kholia/HF-PA-v5/datasheets/5v-regulator-circuit.gif

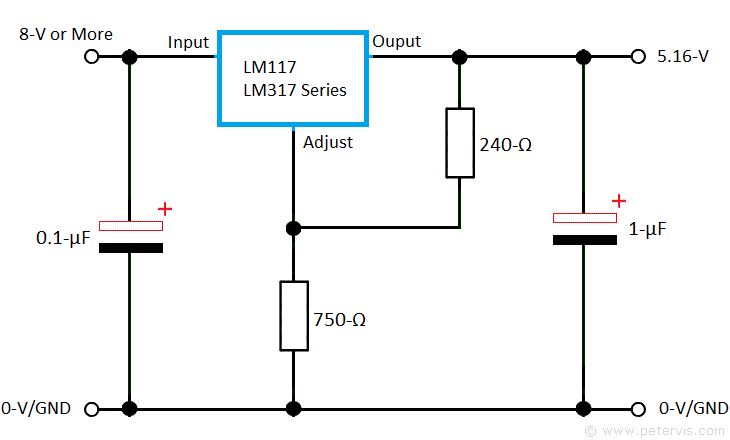
datasheets/5v-regulator-circuit.gif
