kholia/HF-PA-v5/datasheets/irf510-pinout-equivalent.gif

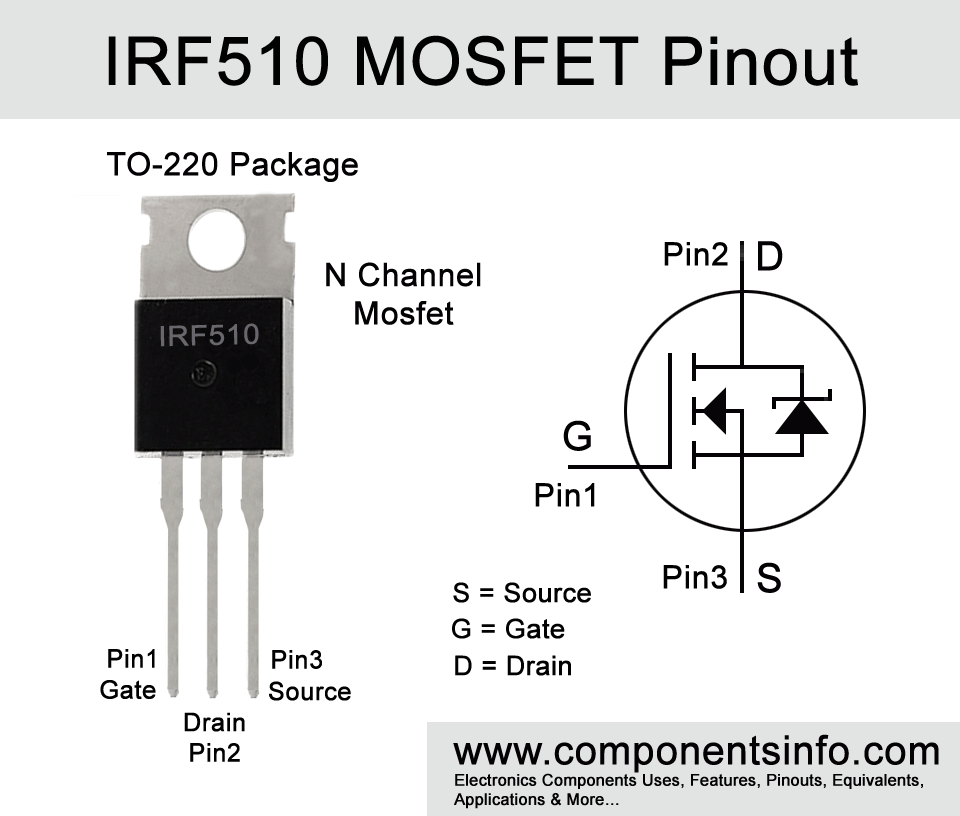
datasheets/irf510-pinout-equivalent.gif
