kholia/HF-PA-v5/datasheets/LM317-voltage-source.png

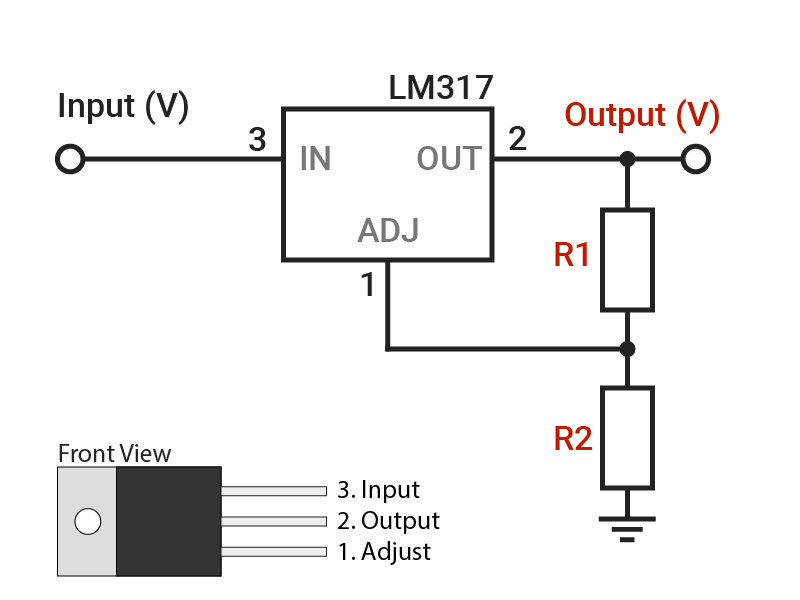
datasheets/LM317-voltage-source.png
