kholia/HF-PA-v5/Info/5W HF PA - Hans.png

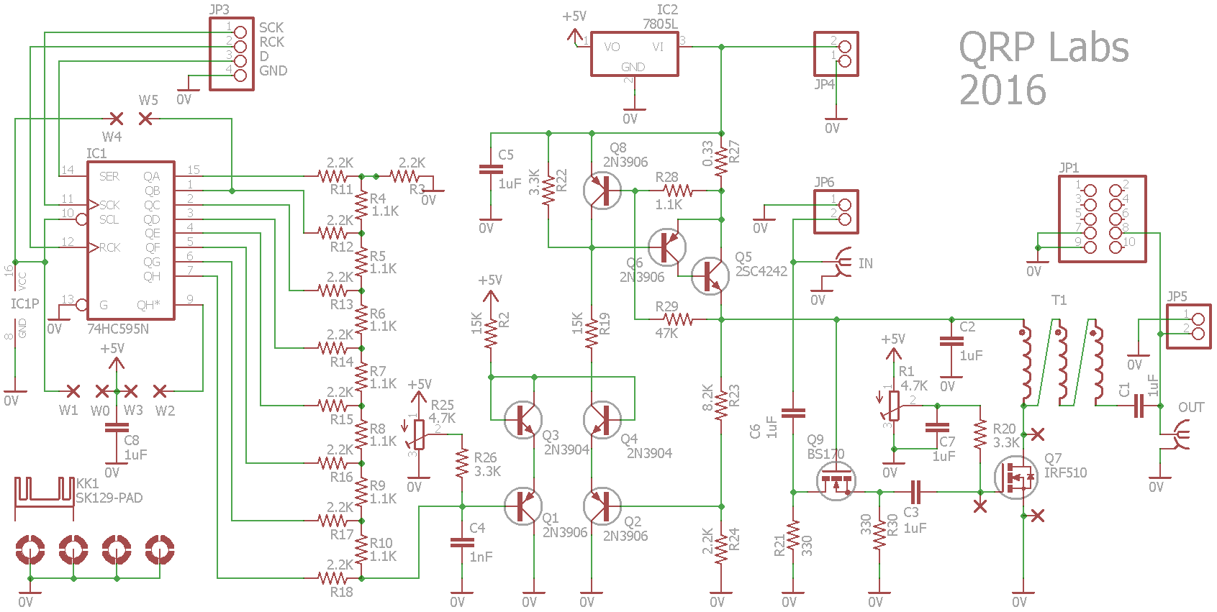
Info/5W HF PA - Hans.png
