kholia/HF-PA-v5/Info/10W HF Linear PA - Hans.png

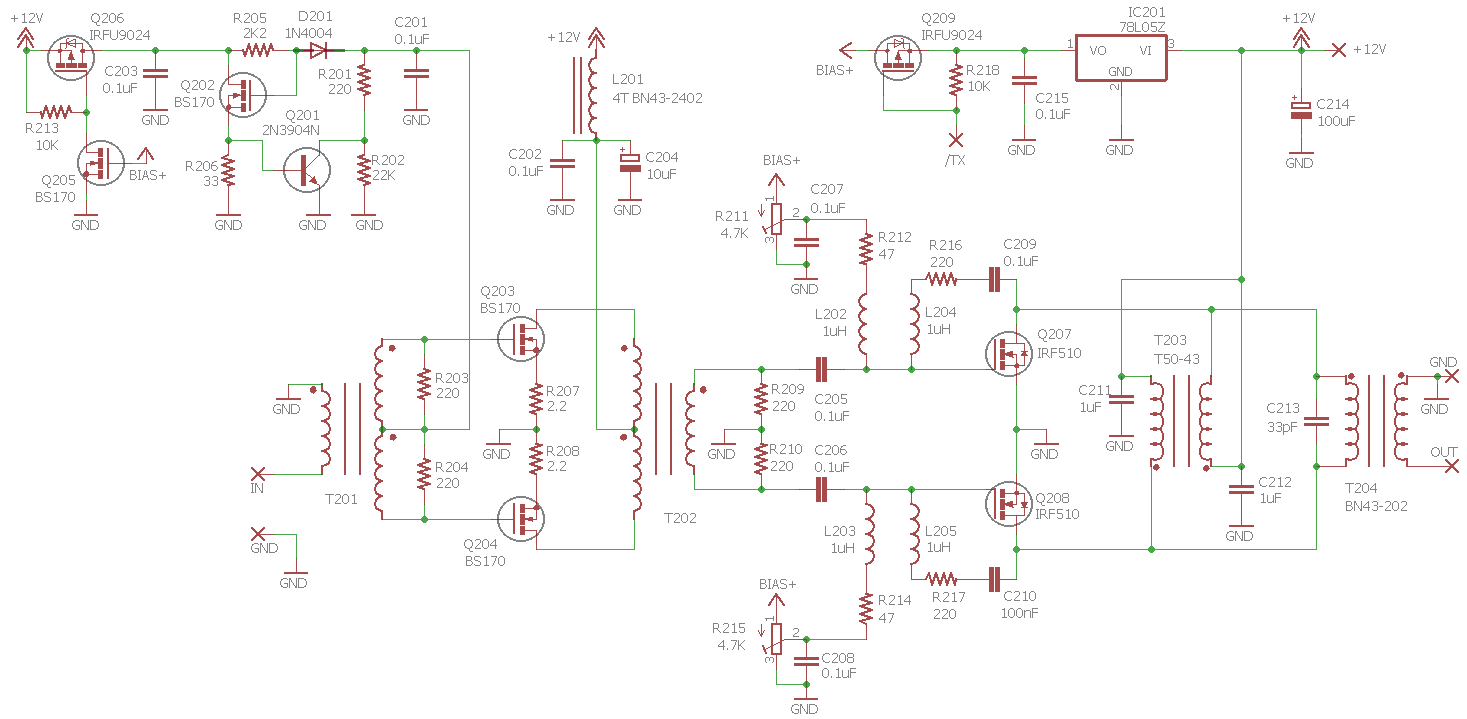
Info/10W HF Linear PA - Hans.png
