kholia/HF-PA-v5/Info/15-02-2021-11-56-602a616ec8522.jpeg

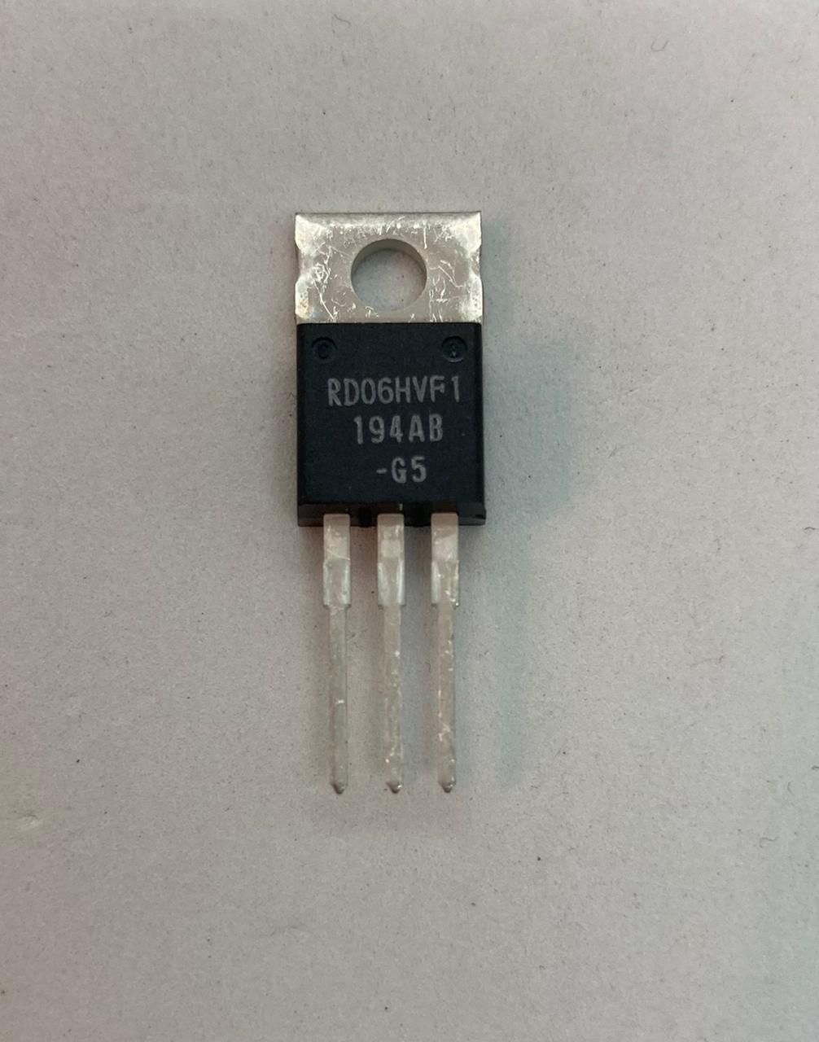
Info/15-02-2021-11-56-602a616ec8522.jpeg
