kholia/HF-PA-v5/Info/15-02-2021-11-57-602a61b2251c0.jpeg

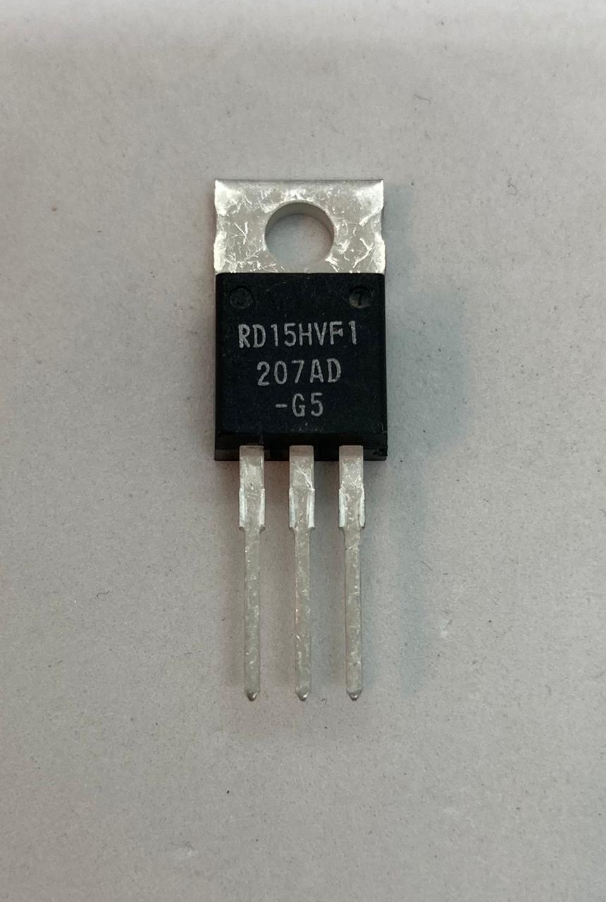
Info/15-02-2021-11-57-602a61b2251c0.jpeg
