kholia/HF-PA-v5/Info/28M5Wamp1.png

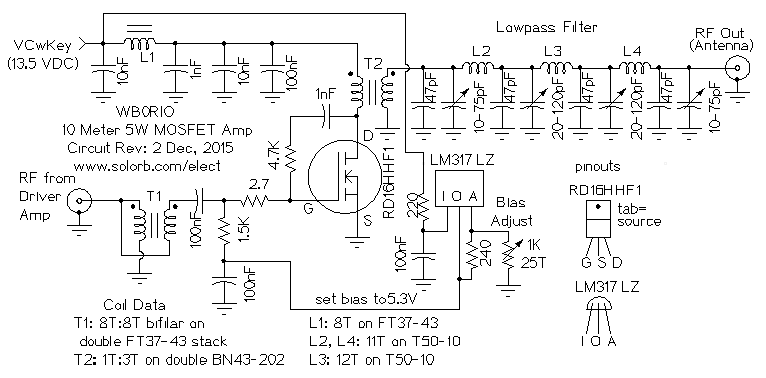
Info/28M5Wamp1.png
