kholia/HF-PA-v5/Info/1367.jpg

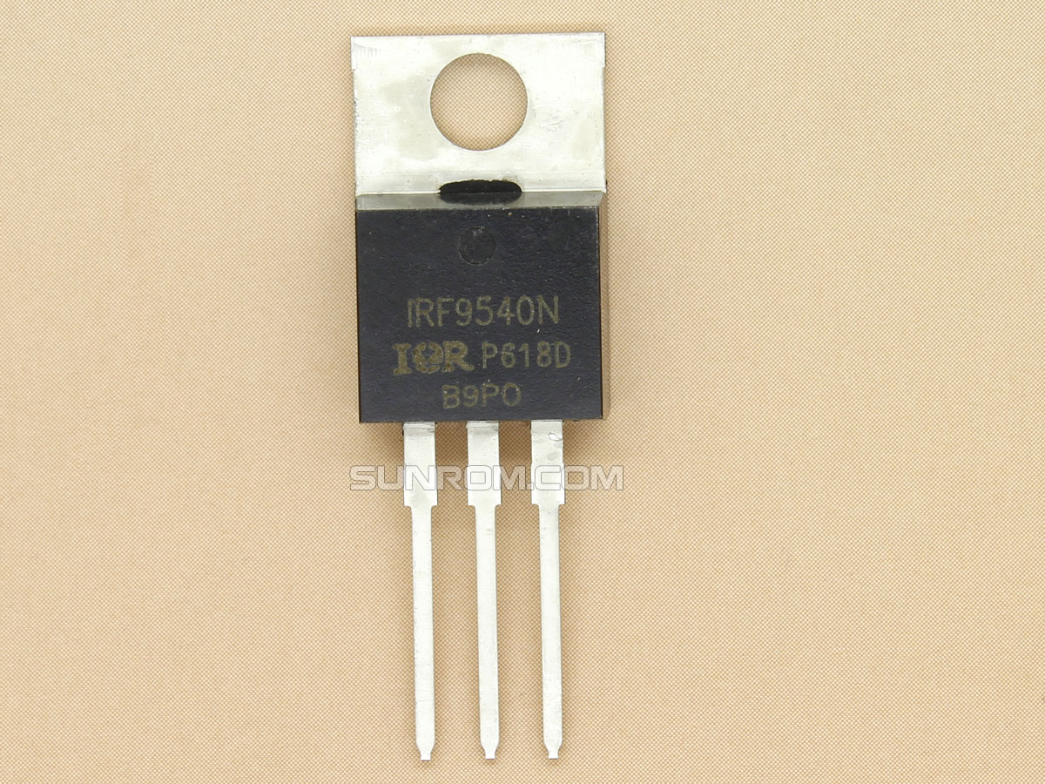
Info/1367.jpg
