kholia/HF-PA-v5/Info/2022-01-05 23.05.50.jpg

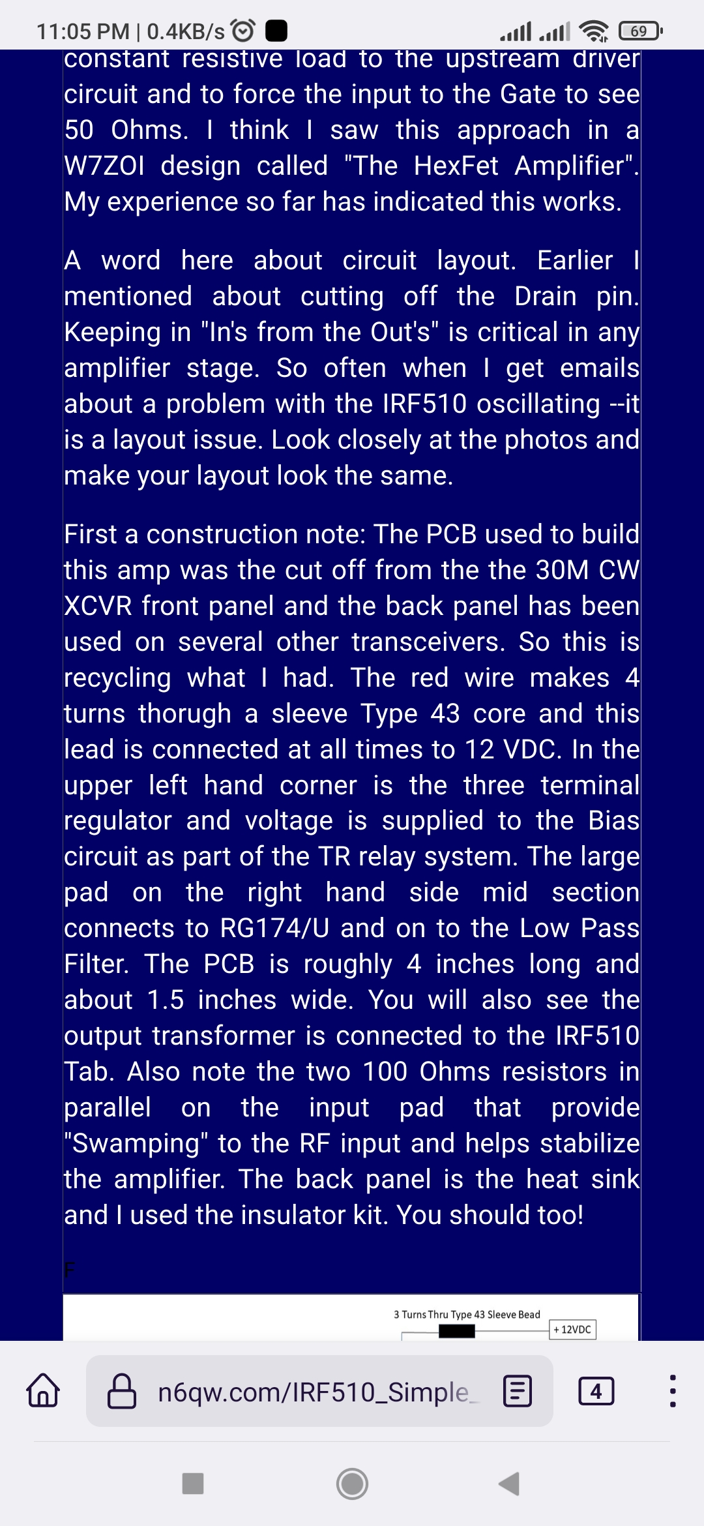
Info/2022-01-05 23.05.50.jpg
