kholia/HF-PA-v5/Info/2022-01-08 22.07.23.jpg

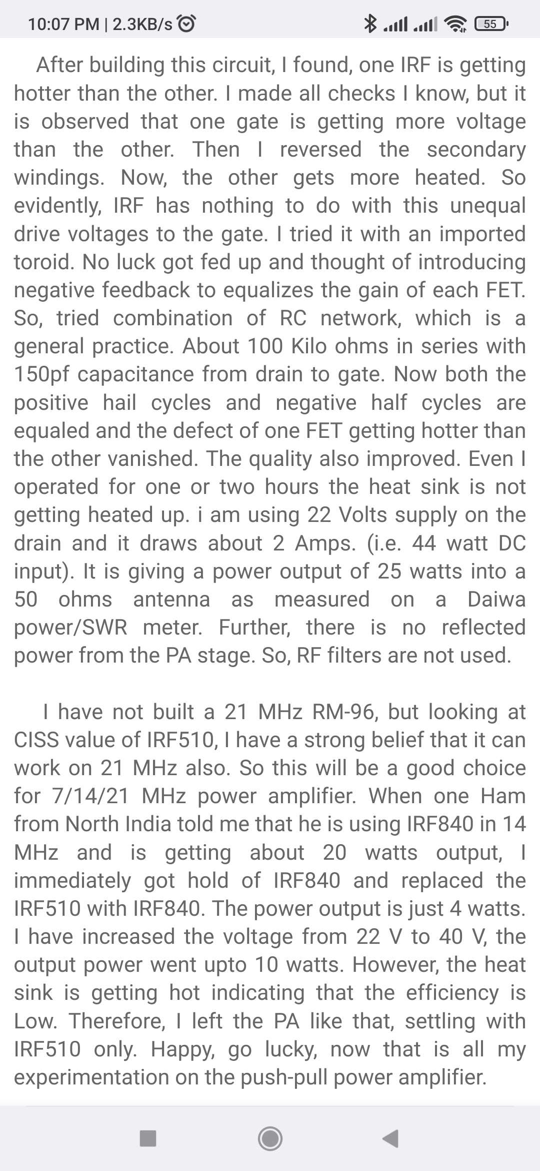
Info/2022-01-08 22.07.23.jpg
