kholia/HF-PA-v5/Info/2022-01-08 22.09.43.jpg

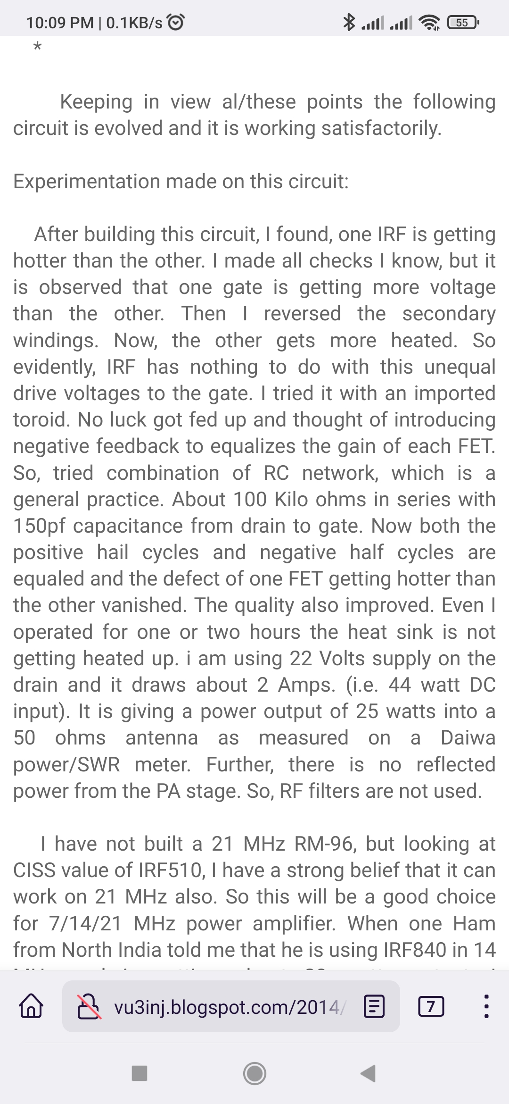
Info/2022-01-08 22.09.43.jpg
