kholia/HF-PA-v5/Info/Aluminium U Type Heat Sink 1.jpg

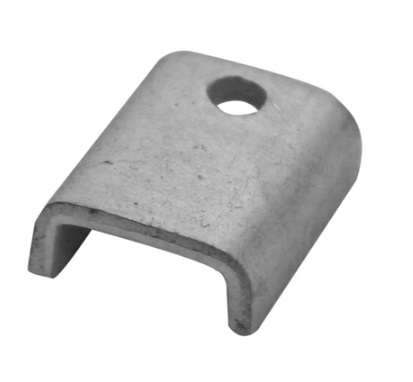
Info/Aluminium U Type Heat Sink 1.jpg
