kholia/HF-PA-v5/Info/Heatsink TO-220.jpg

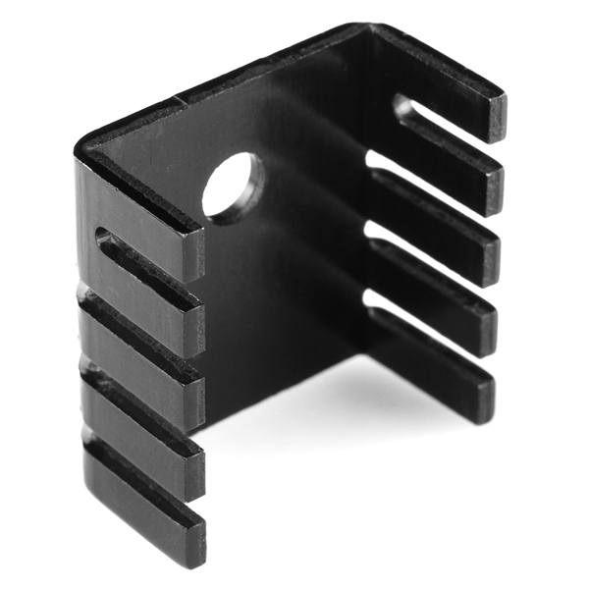
Info/Heatsink TO-220.jpg
