kholia/HF-PA-v5/Info/Hex-Inverter-As-MOSFET-Driver.gif

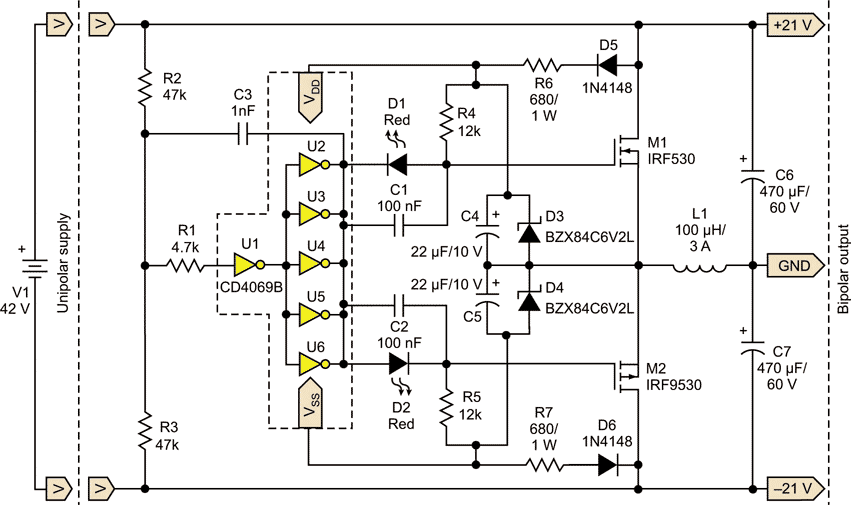
Info/Hex-Inverter-As-MOSFET-Driver.gif
