kholia/HF-PA-v5/Info/Hot mashup idea - was found independently on TG first.png

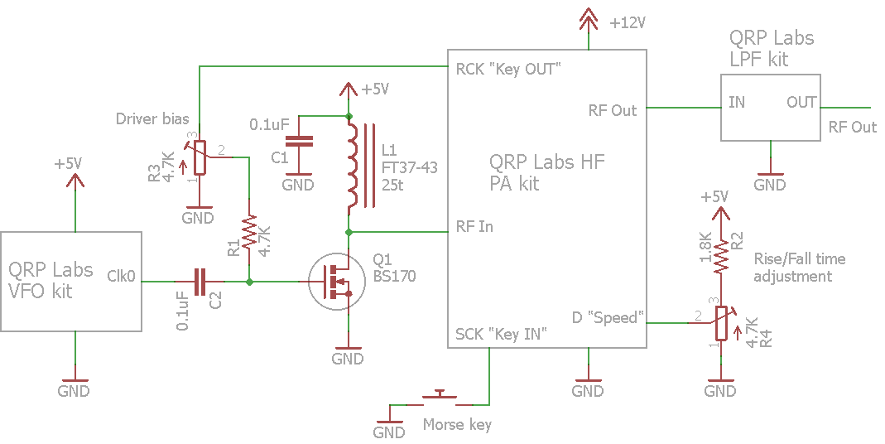
Info/Hot mashup idea - was found independently on TG first.png
