kholia/HF-PA-v5/Info/KB1GMX note.png

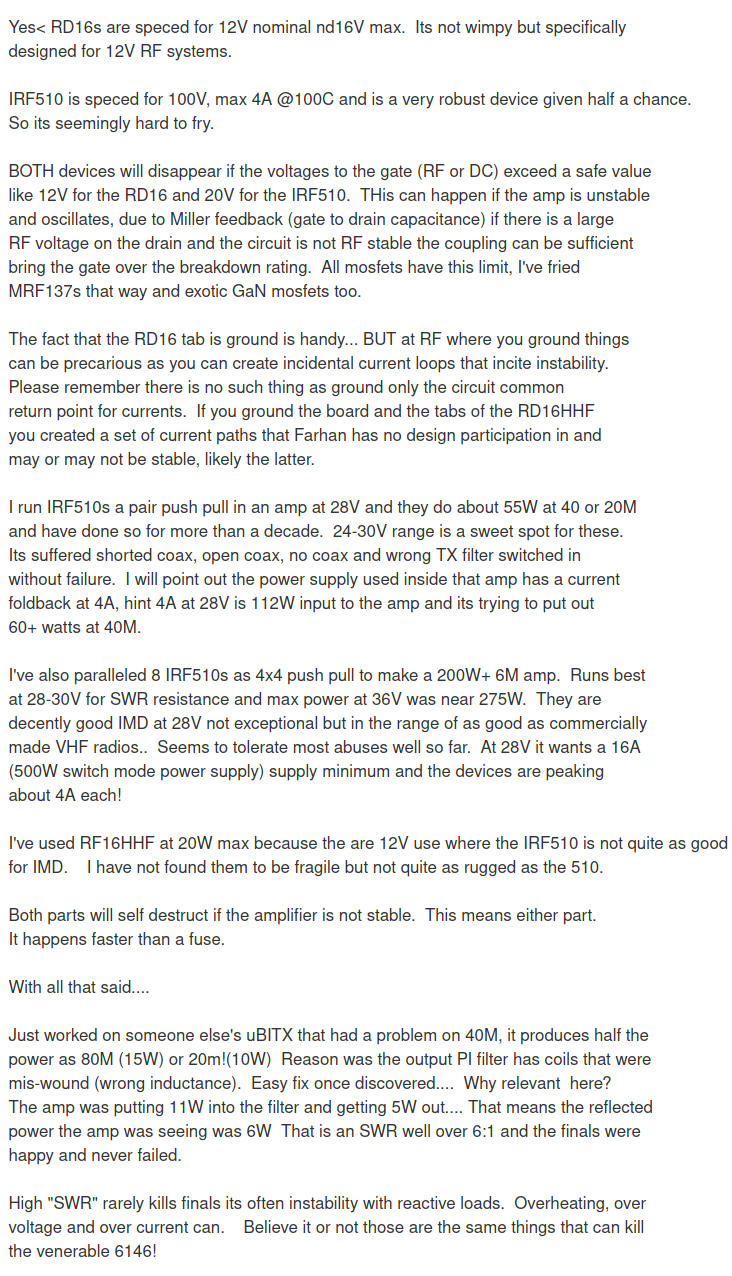
Info/KB1GMX note.png
