kholia/HF-PA-v5/Info/MTR5B PA.png

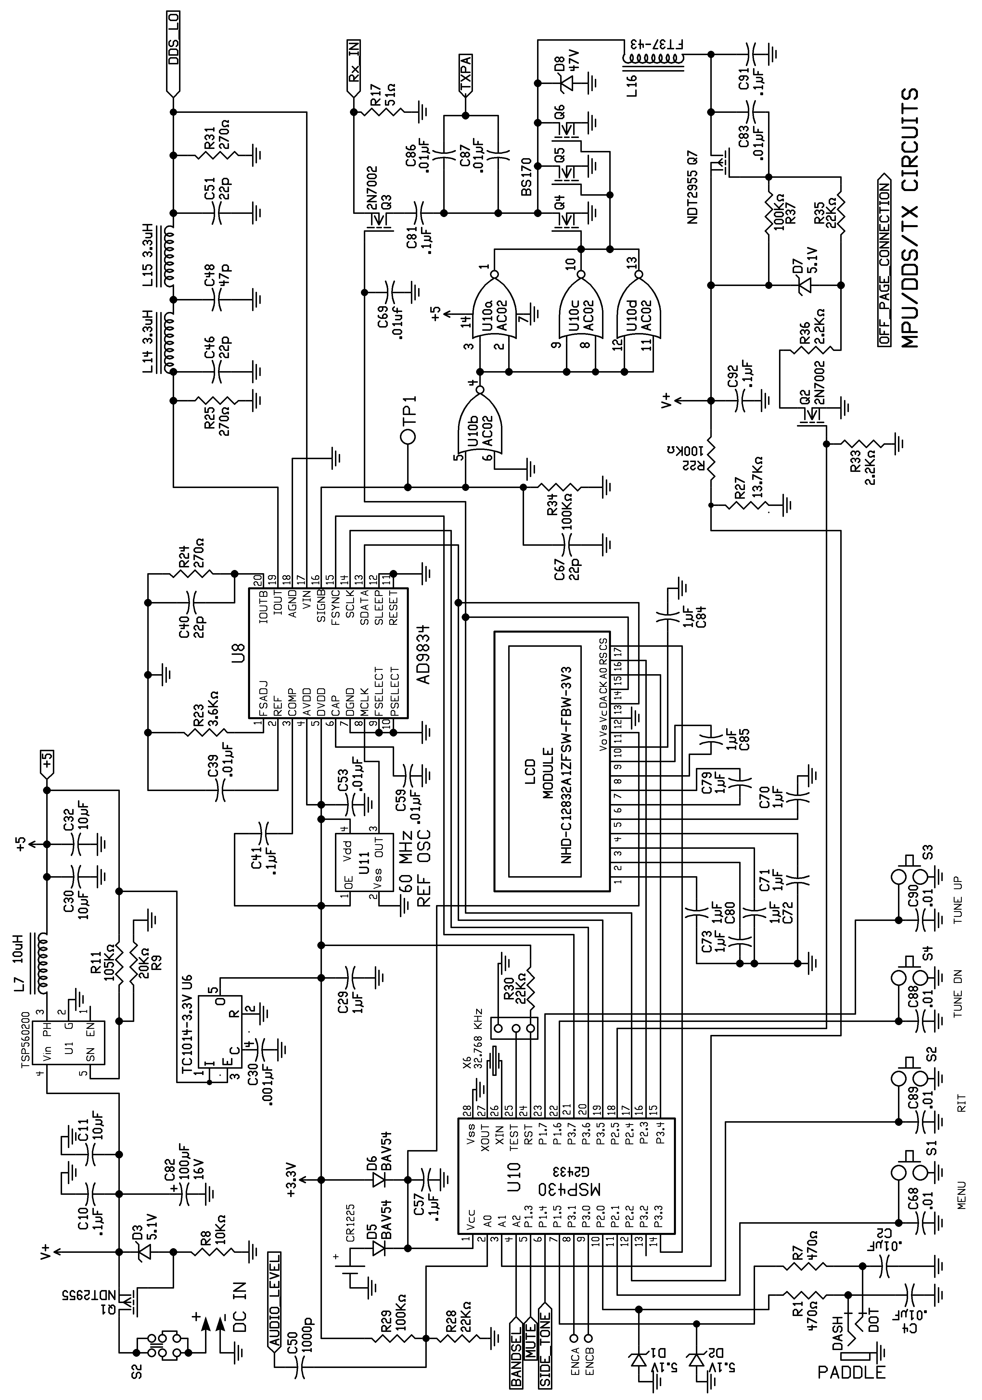
Info/MTR5B PA.png
