kholia/HF-PA-v5/Info/PFR-3-TX.png

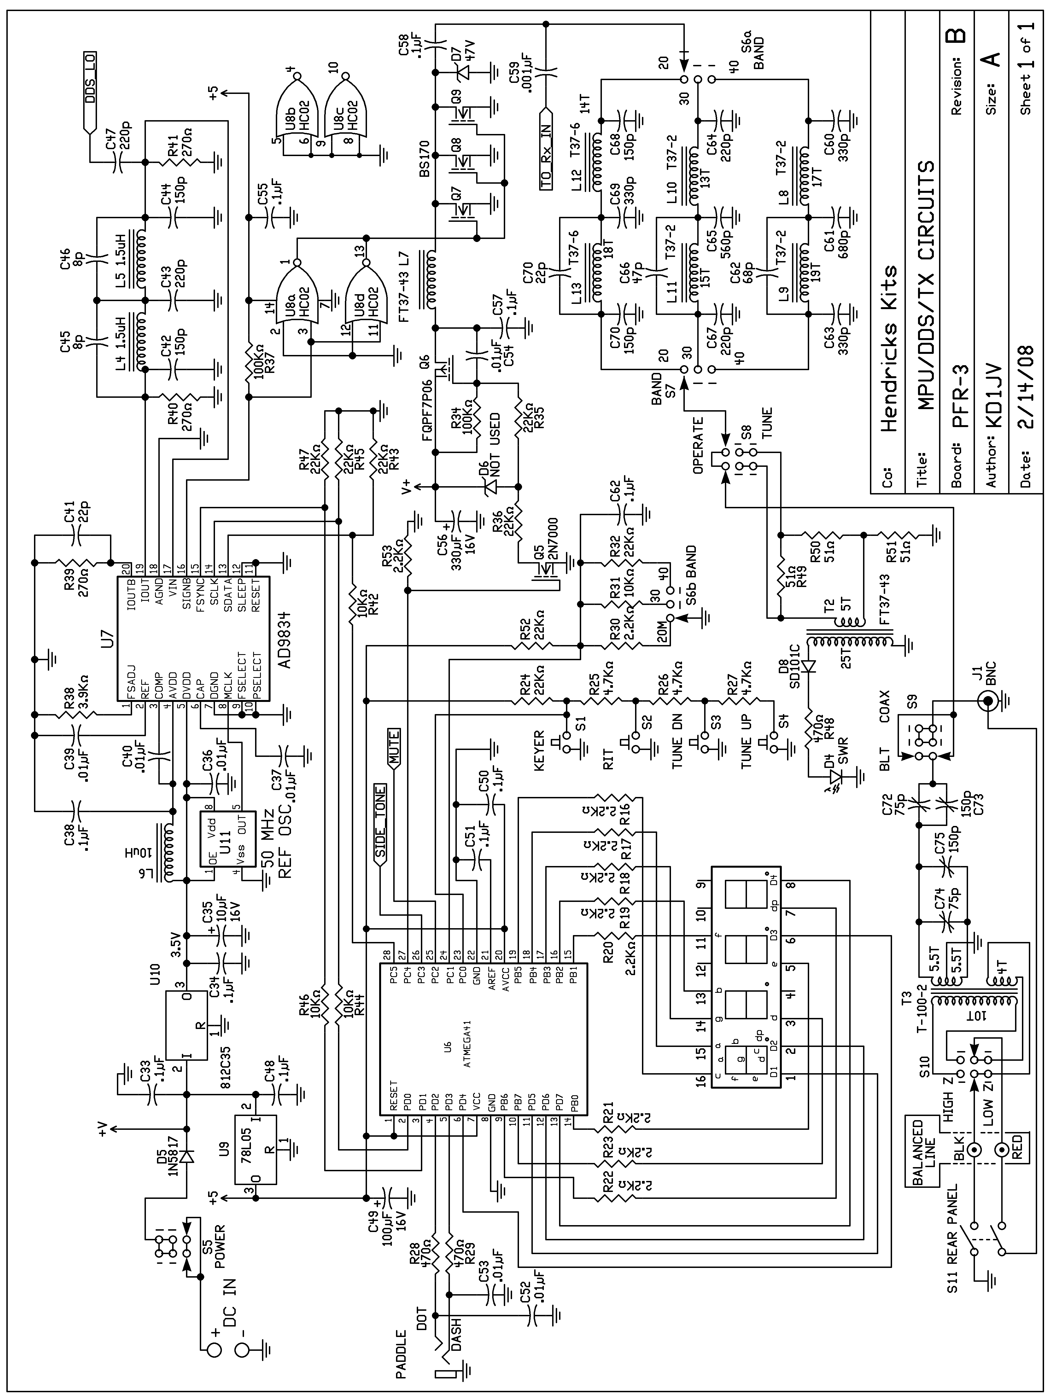
Info/PFR-3-TX.png
