kholia/HF-PA-v5/Info/RM065-672x378.jpg

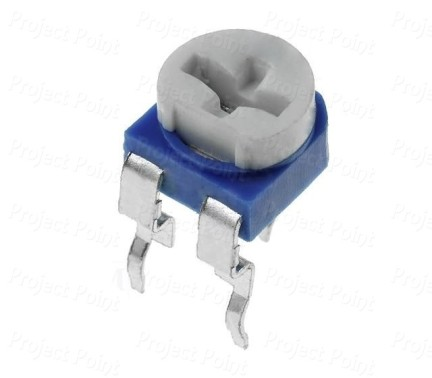
Info/RM065-672x378.jpg
