kholia/HF-PA-v5/Info/Screenshot_2022-01-20_20-48-25.png

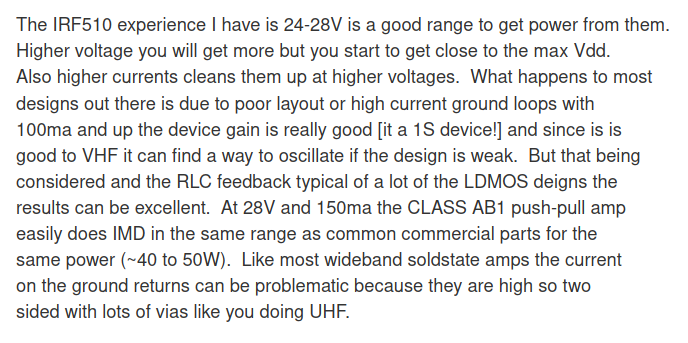
Info/Screenshot_2022-01-20_20-48-25.png
