kholia/HF-PA-v5/Info/Screenshot_2022-03-04_15-51-50.png

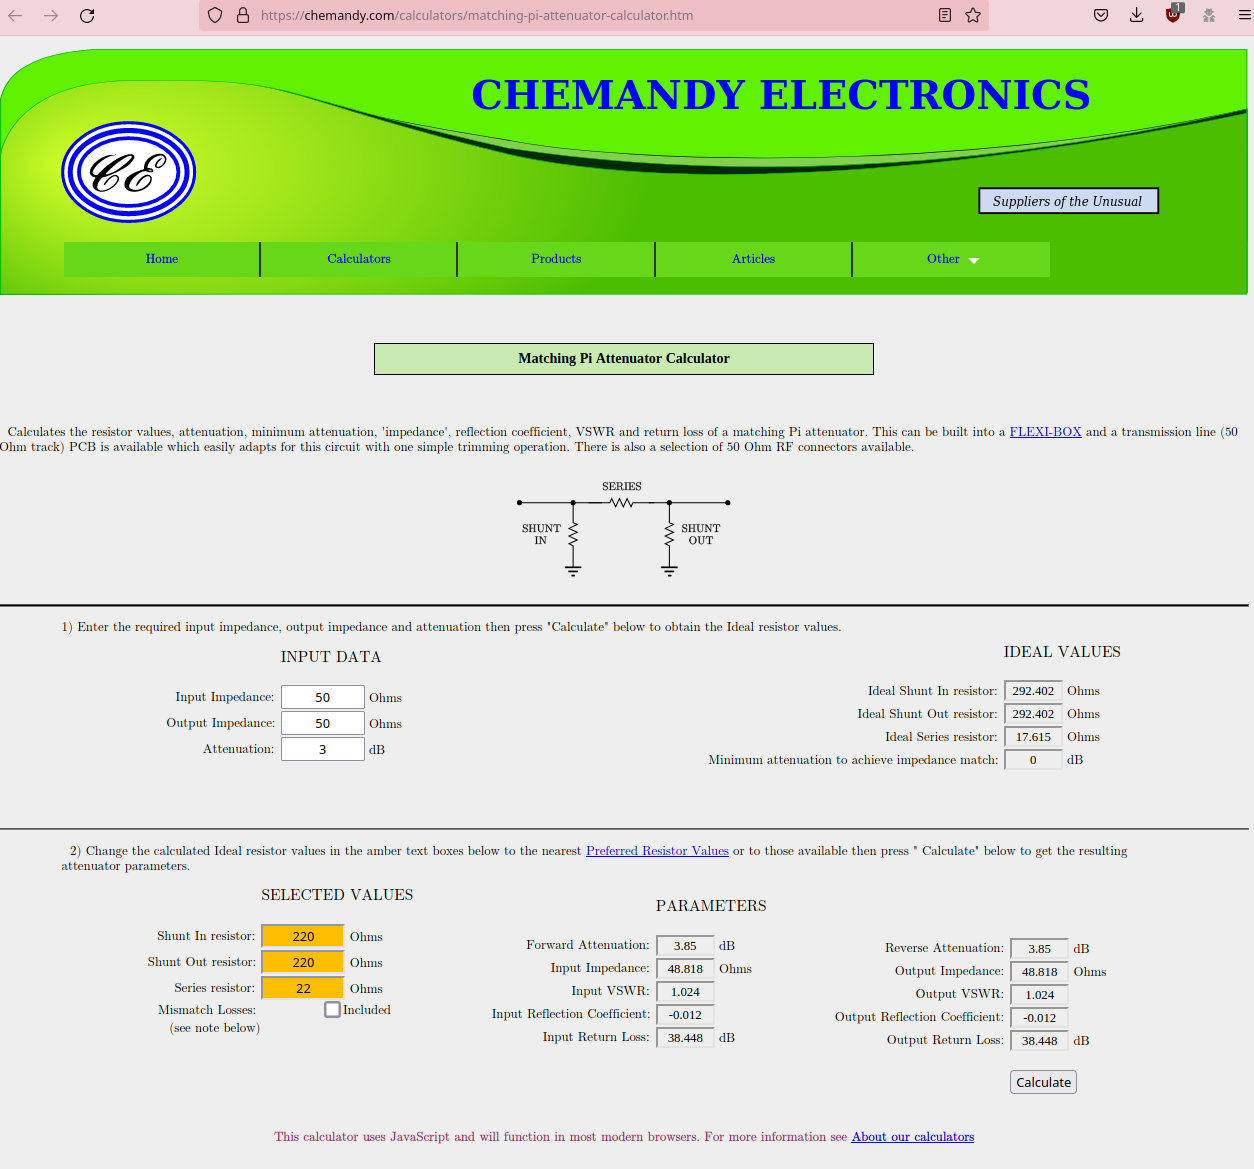
Info/Screenshot_2022-03-04_15-51-50.png
