kholia/HF-PA-v5/Info/Stability-2-ARRL-Chapter-17-2019.png

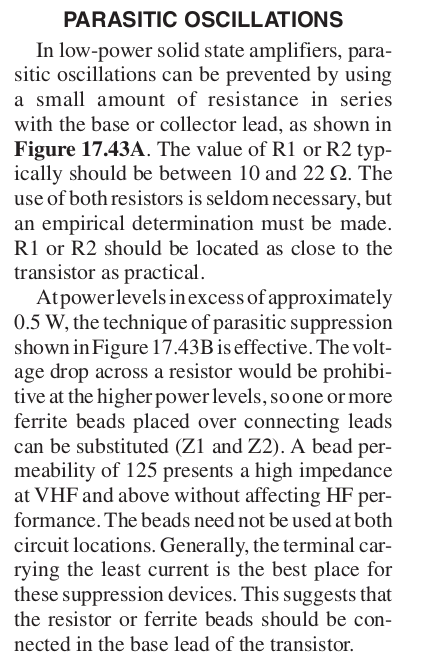
Info/Stability-2-ARRL-Chapter-17-2019.png
