kholia/HF-PA-v5/Info/Stability-ARRL-Screenshot_2022-01-09_15-55-31.png

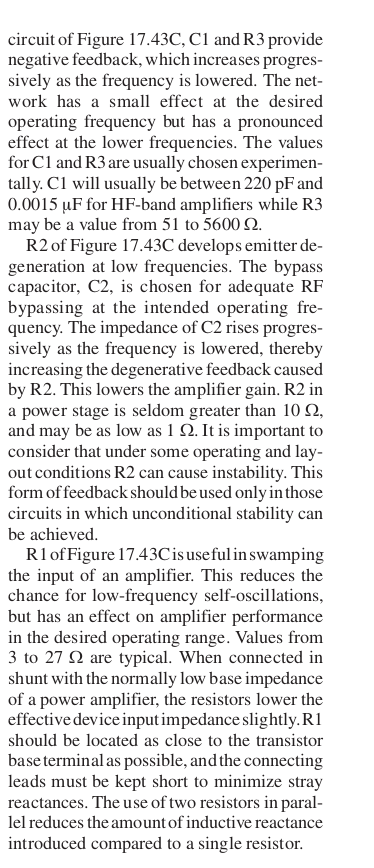
Info/Stability-ARRL-Screenshot_2022-01-09_15-55-31.png
