kholia/HF-PA-v5/Info/Toroid Winding Direction - WB5RVZ.png

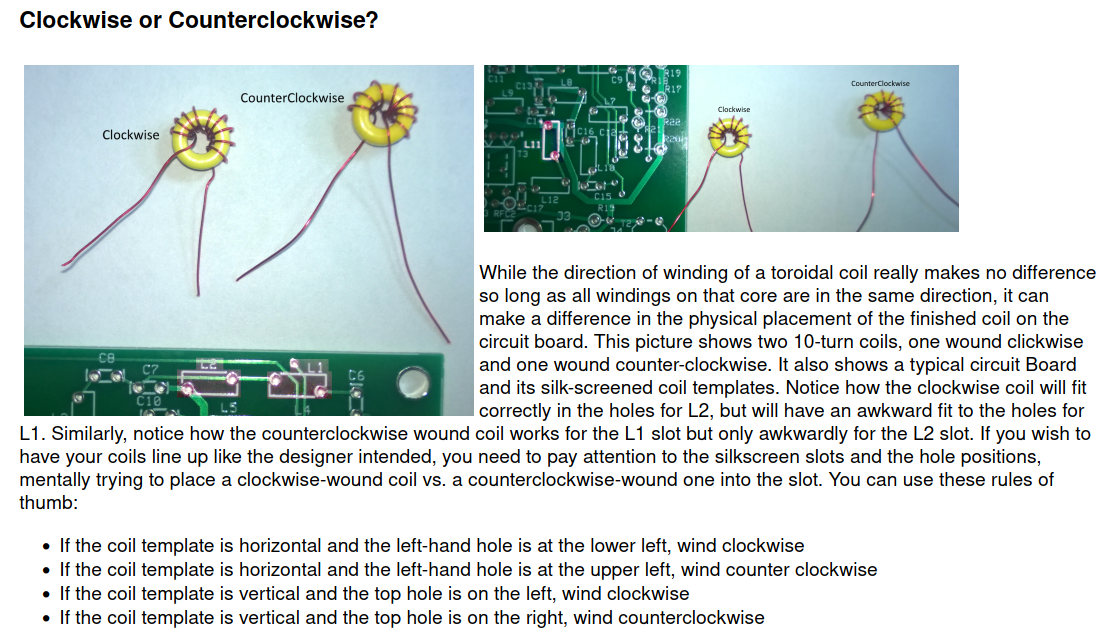
Info/Toroid Winding Direction - WB5RVZ.png
