kholia/HF-PA-v5/Info/uSDXn - Latest 2021.jpg

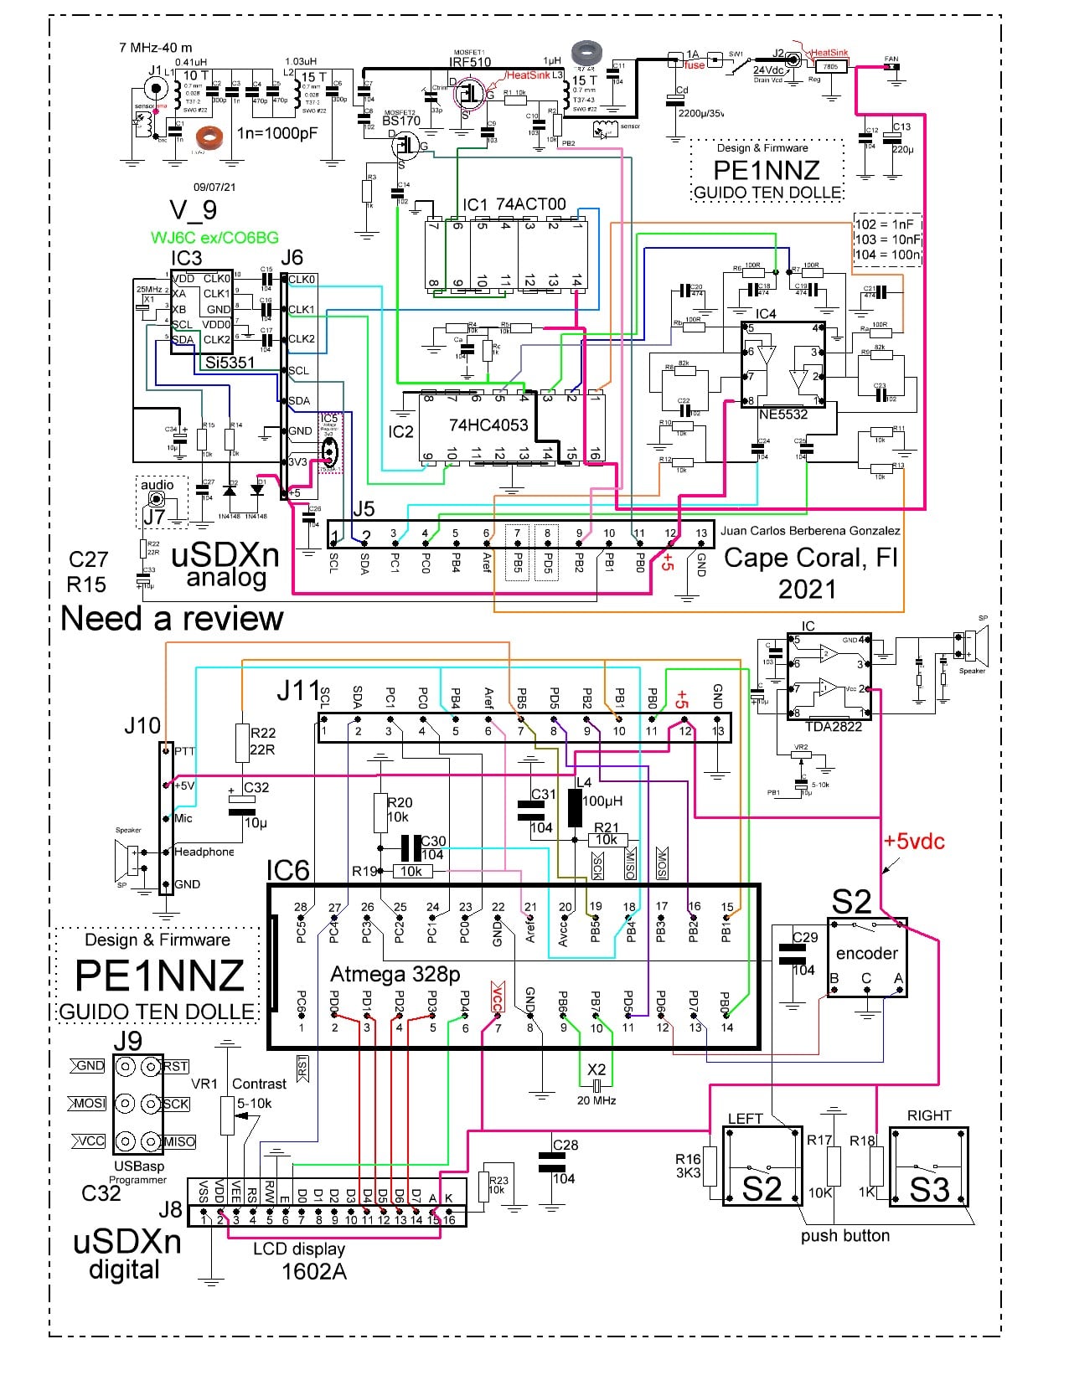
Info/uSDXn - Latest 2021.jpg
