kholia/HF-PA-v5/Info/uSDXN For Novice - PY2OHH.jpg

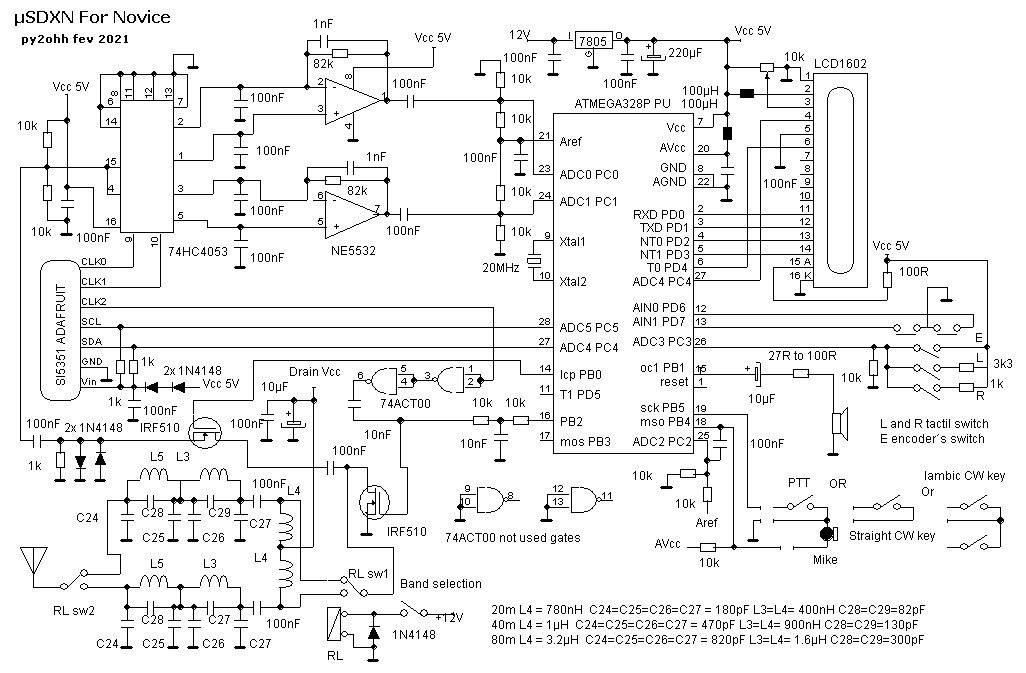
Info/uSDXN For Novice - PY2OHH.jpg
