kholia/HF-PA-v5/Info/WA2EBY-Amp-PCB-1.png

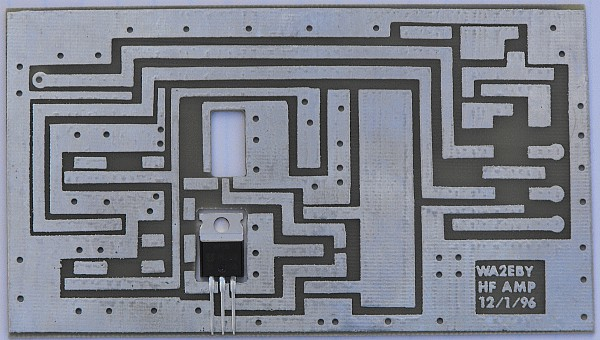
Info/WA2EBY-Amp-PCB-1.png
