kholia/HF-PA-v5/Wider-LPF-QUCS/F1.png

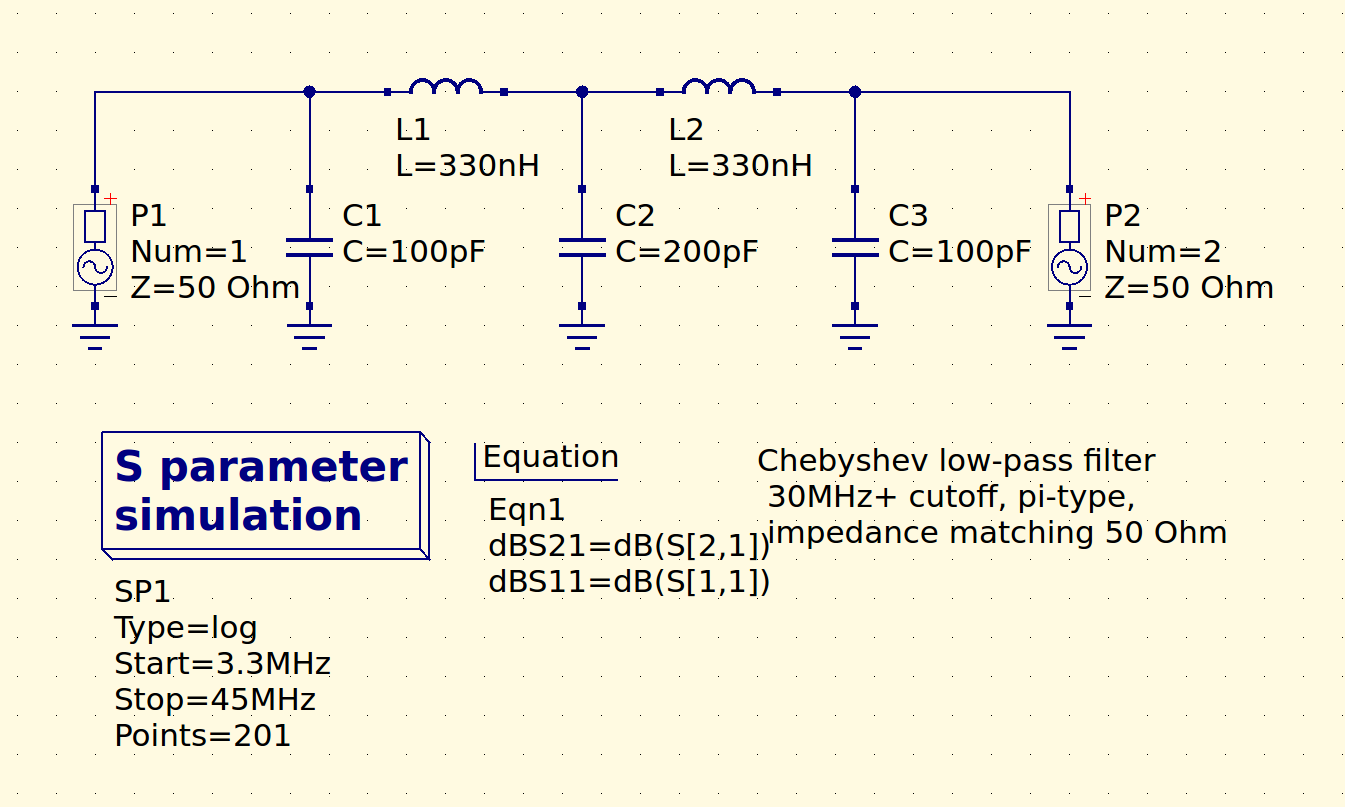
Wider-LPF-QUCS/F1.png
