kholia/HF-PA-v5/Wider-LPF-QUCS/F2.png

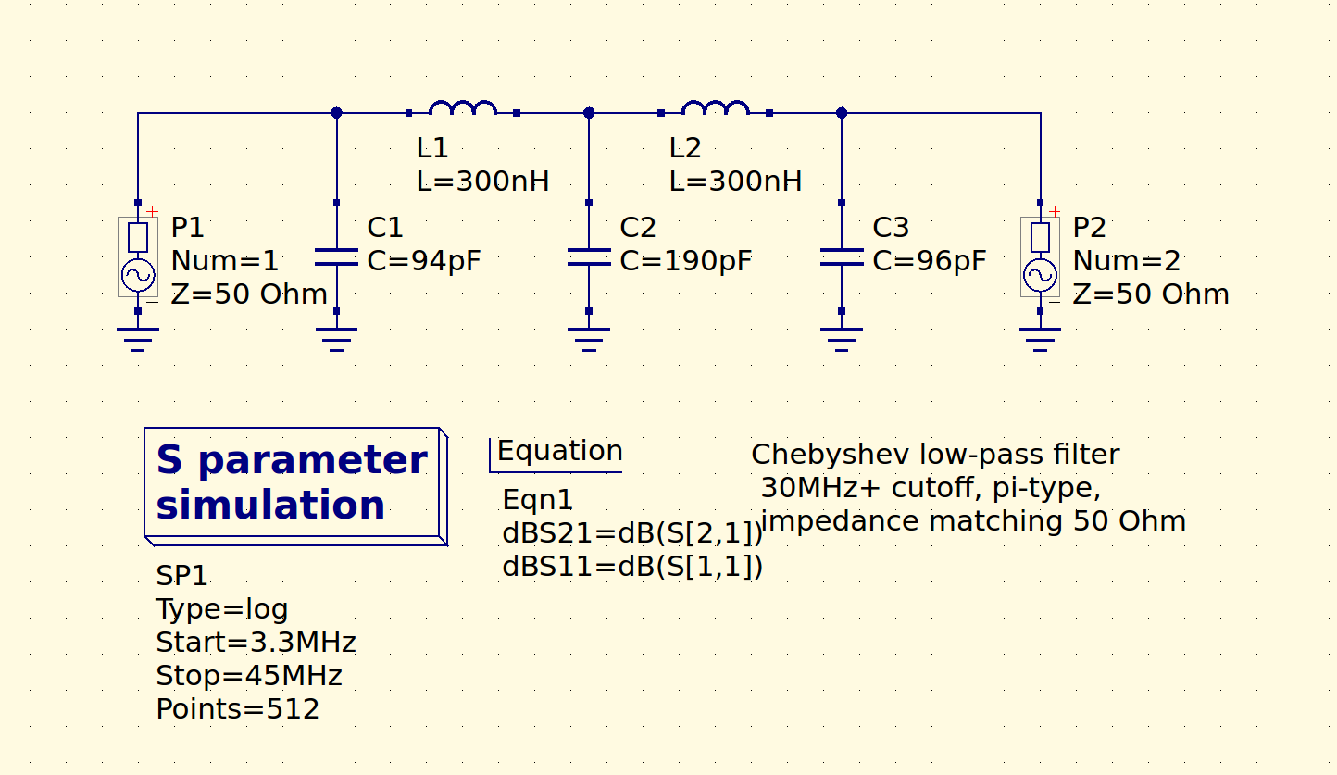
Wider-LPF-QUCS/F2.png
