kholia/HF-PA-v5/Info/RD(xy) test from John.jpeg

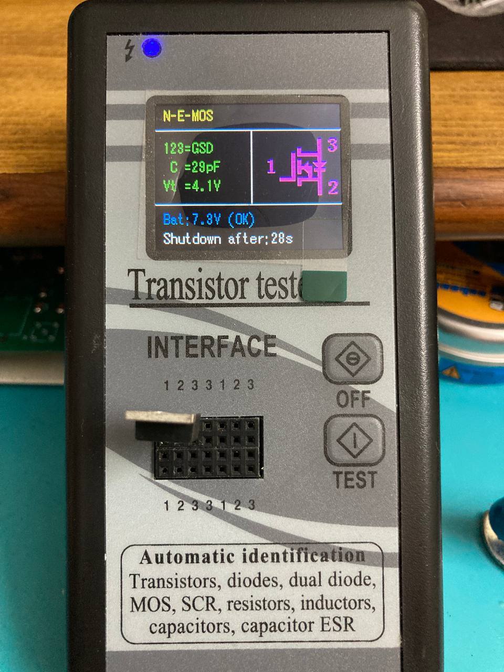
Info/RD(xy) test from John.jpeg
