kholia/HF-PA-v5/Wider-LPF-QUCS/Validation - Screenshot_2021-10-15_14-24-16.png

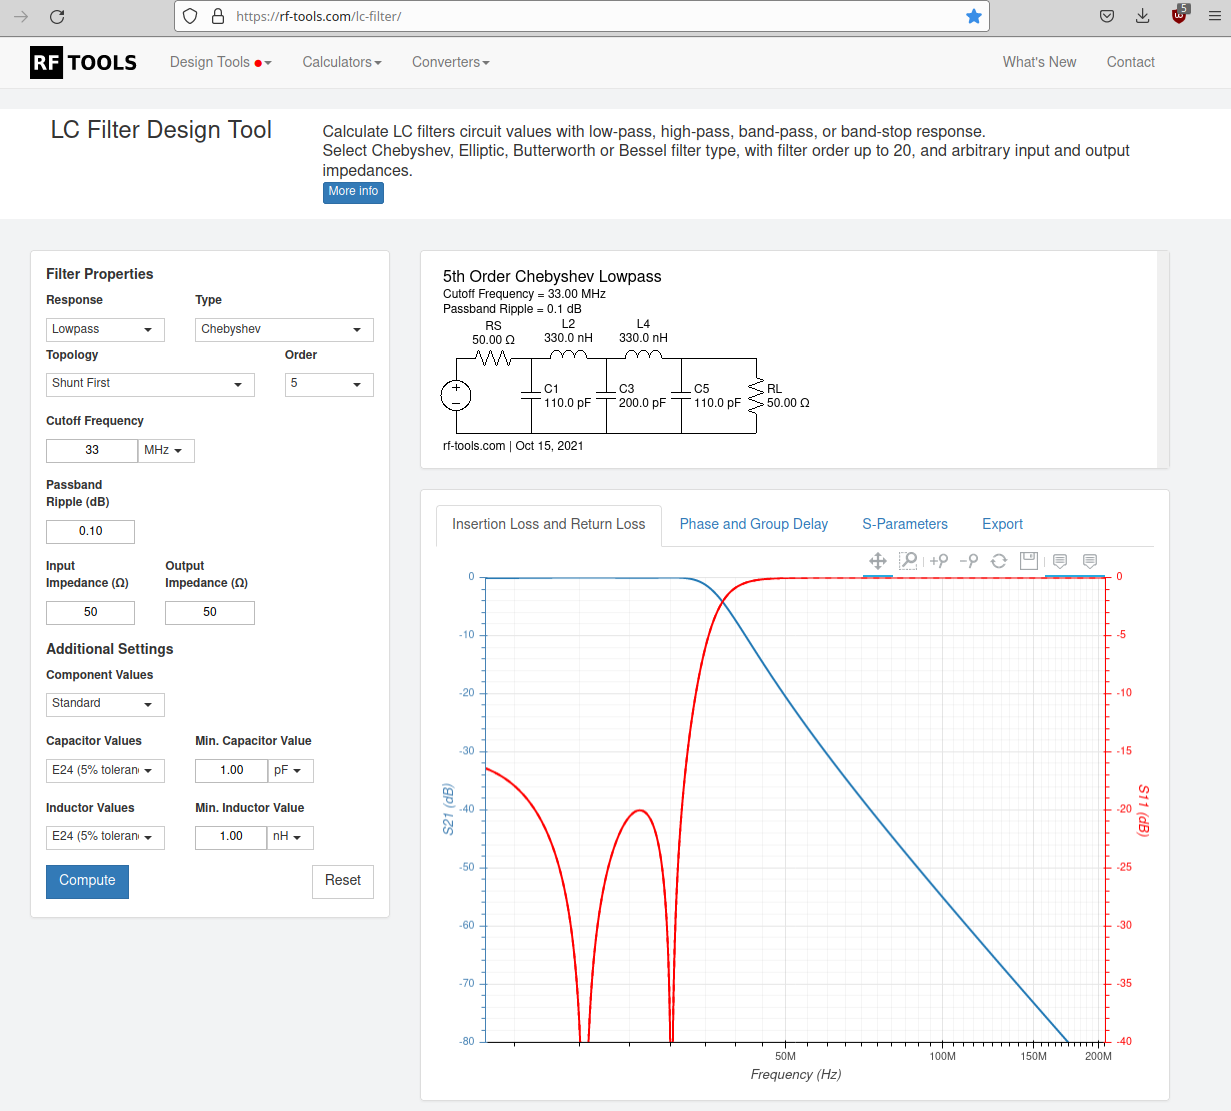
Wider-LPF-QUCS/Validation - Screenshot_2021-10-15_14-24-16.png
